MelkhiorVintageComputing/IIsiFPGA/IIsi-to-ztex-gateware/FPMult_15_63_uid2_Freq300_uid3.vhdl

--------------------------------------------------------------------------------
--                       Compressor_23_3_Freq300_uid32
-- VHDL generated for Kintex7 @ 300MHz
-- This operator is part of the Infinite Virtual Library FloPoCoLib
-- All rights reserved 
-- Authors: 
--------------------------------------------------------------------------------
-- combinatorial
-- Clock period (ns): 3.33333
-- Target frequency (MHz): 300
-- Input signals: X1 X0
-- Output signals: R

library ieee;
use ieee.std_logic_1164.all;
use ieee.std_logic_arith.all;
use ieee.std_logic_unsigned.all;
library std;
use std.textio.all;
library work;

entity Compressor_23_3_Freq300_uid32 is
    port (X1 : in  std_logic_vector(1 downto 0);
          X0 : in  std_logic_vector(2 downto 0);
          R : out  std_logic_vector(2 downto 0)   );
end entity;

architecture arch of Compressor_23_3_Freq300_uid32 is
signal X :  std_logic_vector(4 downto 0);
signal R0 :  std_logic_vector(2 downto 0);
begin
   X <= X1 & X0 ;

   with X  select  R0 <= 
      "000" when "00000",
      "001" when "00001" | "00010" | "00100",
      "010" when "00011" | "00101" | "00110" | "01000" | "10000",
      "011" when "00111" | "01001" | "01010" | "01100" | "10001" | "10010" | "10100",
      "100" when "01011" | "01101" | "01110" | "10011" | "10101" | "10110" | "11000",
      "101" when "01111" | "10111" | "11001" | "11010" | "11100",
      "110" when "11011" | "11101" | "11110",
      "111" when "11111",
      "---" when others;
   R <= R0;
end architecture;

--------------------------------------------------------------------------------
--                        Compressor_3_2_Freq300_uid40
-- VHDL generated for Kintex7 @ 300MHz
-- This operator is part of the Infinite Virtual Library FloPoCoLib
-- All rights reserved 
-- Authors: 
--------------------------------------------------------------------------------
-- combinatorial
-- Clock period (ns): 3.33333
-- Target frequency (MHz): 300
-- Input signals: X0
-- Output signals: R

library ieee;
use ieee.std_logic_1164.all;
use ieee.std_logic_arith.all;
use ieee.std_logic_unsigned.all;
library std;
use std.textio.all;
library work;

entity Compressor_3_2_Freq300_uid40 is
    port (X0 : in  std_logic_vector(2 downto 0);
          R : out  std_logic_vector(1 downto 0)   );
end entity;

architecture arch of Compressor_3_2_Freq300_uid40 is
signal X :  std_logic_vector(2 downto 0);
signal R0 :  std_logic_vector(1 downto 0);
begin
   X <= X0 ;

   with X  select  R0 <= 
      "00" when "000",
      "01" when "001" | "010" | "100",
      "10" when "011" | "101" | "110",
      "11" when "111",
      "--" when others;
   R <= R0;
end architecture;

--------------------------------------------------------------------------------
--                       Compressor_14_3_Freq300_uid54
-- VHDL generated for Kintex7 @ 300MHz
-- This operator is part of the Infinite Virtual Library FloPoCoLib
-- All rights reserved 
-- Authors: 
--------------------------------------------------------------------------------
-- combinatorial
-- Clock period (ns): 3.33333
-- Target frequency (MHz): 300
-- Input signals: X1 X0
-- Output signals: R

library ieee;
use ieee.std_logic_1164.all;
use ieee.std_logic_arith.all;
use ieee.std_logic_unsigned.all;
library std;
use std.textio.all;
library work;

entity Compressor_14_3_Freq300_uid54 is
    port (X1 : in  std_logic_vector(0 downto 0);
          X0 : in  std_logic_vector(3 downto 0);
          R : out  std_logic_vector(2 downto 0)   );
end entity;

architecture arch of Compressor_14_3_Freq300_uid54 is
signal X :  std_logic_vector(4 downto 0);
signal R0 :  std_logic_vector(2 downto 0);
begin
   X <= X1 & X0 ;

   with X  select  R0 <= 
      "000" when "00000",
      "001" when "00001" | "00010" | "00100" | "01000",
      "010" when "00011" | "00101" | "00110" | "01001" | "01010" | "01100" | "10000",
      "011" when "00111" | "01011" | "01101" | "01110" | "10001" | "10010" | "10100" | "11000",
      "100" when "01111" | "10011" | "10101" | "10110" | "11001" | "11010" | "11100",
      "101" when "10111" | "11011" | "11101" | "11110",
      "110" when "11111",
      "---" when others;
   R <= R0;
end architecture;

--------------------------------------------------------------------------------
--                        Compressor_6_3_Freq300_uid90
-- VHDL generated for Kintex7 @ 300MHz
-- This operator is part of the Infinite Virtual Library FloPoCoLib
-- All rights reserved 
-- Authors: 
--------------------------------------------------------------------------------
-- combinatorial
-- Clock period (ns): 3.33333
-- Target frequency (MHz): 300
-- Input signals: X0
-- Output signals: R

library ieee;
use ieee.std_logic_1164.all;
use ieee.std_logic_arith.all;
use ieee.std_logic_unsigned.all;
library std;
use std.textio.all;
library work;

entity Compressor_6_3_Freq300_uid90 is
    port (X0 : in  std_logic_vector(5 downto 0);
          R : out  std_logic_vector(2 downto 0)   );
end entity;

architecture arch of Compressor_6_3_Freq300_uid90 is
signal X :  std_logic_vector(5 downto 0);
signal R0 :  std_logic_vector(2 downto 0);
begin
   X <= X0 ;

   with X  select  R0 <= 
      "000" when "000000",
      "001" when "000001" | "000010" | "000100" | "001000" | "010000" | "100000",
      "010" when "000011" | "000101" | "000110" | "001001" | "001010" | "001100" | "010001" | "010010" | "010100" | "011000" | "100001" | "100010" | "100100" | "101000" | "110000",
      "011" when "000111" | "001011" | "001101" | "001110" | "010011" | "010101" | "010110" | "011001" | "011010" | "011100" | "100011" | "100101" | "100110" | "101001" | "101010" | "101100" | "110001" | "110010" | "110100" | "111000",
      "100" when "001111" | "010111" | "011011" | "011101" | "011110" | "100111" | "101011" | "101101" | "101110" | "110011" | "110101" | "110110" | "111001" | "111010" | "111100",
      "101" when "011111" | "101111" | "110111" | "111011" | "111101" | "111110",
      "110" when "111111",
      "---" when others;
   R <= R0;
end architecture;

--------------------------------------------------------------------------------
--                        DSPBlock_24x17_Freq300_uid9
-- VHDL generated for Kintex7 @ 300MHz
-- This operator is part of the Infinite Virtual Library FloPoCoLib
-- All rights reserved 
-- Authors: 
--------------------------------------------------------------------------------
-- Pipeline depth: 0 cycles
-- Clock period (ns): 3.33333
-- Target frequency (MHz): 300
-- Input signals: X Y
-- Output signals: R

library ieee;
use ieee.std_logic_1164.all;
use ieee.numeric_std.all;
library std;
use std.textio.all;
library work;

entity DSPBlock_24x17_Freq300_uid9 is
    port (clk : in std_logic;
          X : in  std_logic_vector(23 downto 0);
          Y : in  std_logic_vector(16 downto 0);
          R : out  std_logic_vector(40 downto 0)   );
end entity;

architecture arch of DSPBlock_24x17_Freq300_uid9 is
signal Mfull :  std_logic_vector(40 downto 0);
signal M :  std_logic_vector(40 downto 0);
begin
   Mfull <= std_logic_vector(unsigned(X) * unsigned(Y)); -- multiplier
   M <= Mfull(40 downto 0);
   R <= M;
end architecture;

--------------------------------------------------------------------------------
--                        DSPBlock_24x17_Freq300_uid11
-- VHDL generated for Kintex7 @ 300MHz
-- This operator is part of the Infinite Virtual Library FloPoCoLib
-- All rights reserved 
-- Authors: 
--------------------------------------------------------------------------------
-- Pipeline depth: 0 cycles
-- Clock period (ns): 3.33333
-- Target frequency (MHz): 300
-- Input signals: X Y
-- Output signals: R

library ieee;
use ieee.std_logic_1164.all;
use ieee.numeric_std.all;
library std;
use std.textio.all;
library work;

entity DSPBlock_24x17_Freq300_uid11 is
    port (clk : in std_logic;
          X : in  std_logic_vector(23 downto 0);
          Y : in  std_logic_vector(16 downto 0);
          R : out  std_logic_vector(40 downto 0)   );
end entity;

architecture arch of DSPBlock_24x17_Freq300_uid11 is
signal Mfull :  std_logic_vector(40 downto 0);
signal M :  std_logic_vector(40 downto 0);
begin
   Mfull <= std_logic_vector(unsigned(X) * unsigned(Y)); -- multiplier
   M <= Mfull(40 downto 0);
   R <= M;
end architecture;

--------------------------------------------------------------------------------
--                        DSPBlock_24x17_Freq300_uid13
-- VHDL generated for Kintex7 @ 300MHz
-- This operator is part of the Infinite Virtual Library FloPoCoLib
-- All rights reserved 
-- Authors: 
--------------------------------------------------------------------------------
-- Pipeline depth: 0 cycles
-- Clock period (ns): 3.33333
-- Target frequency (MHz): 300
-- Input signals: X Y
-- Output signals: R

library ieee;
use ieee.std_logic_1164.all;
use ieee.numeric_std.all;
library std;
use std.textio.all;
library work;

entity DSPBlock_24x17_Freq300_uid13 is
    port (clk : in std_logic;
          X : in  std_logic_vector(23 downto 0);
          Y : in  std_logic_vector(16 downto 0);
          R : out  std_logic_vector(40 downto 0)   );
end entity;

architecture arch of DSPBlock_24x17_Freq300_uid13 is
signal Mfull :  std_logic_vector(40 downto 0);
signal M :  std_logic_vector(40 downto 0);
begin
   Mfull <= std_logic_vector(unsigned(X) * unsigned(Y)); -- multiplier
   M <= Mfull(40 downto 0);
   R <= M;
end architecture;

--------------------------------------------------------------------------------
--                        DSPBlock_24x17_Freq300_uid15
-- VHDL generated for Kintex7 @ 300MHz
-- This operator is part of the Infinite Virtual Library FloPoCoLib
-- All rights reserved 
-- Authors: 
--------------------------------------------------------------------------------
-- Pipeline depth: 0 cycles
-- Clock period (ns): 3.33333
-- Target frequency (MHz): 300
-- Input signals: X Y
-- Output signals: R

library ieee;
use ieee.std_logic_1164.all;
use ieee.numeric_std.all;
library std;
use std.textio.all;
library work;

entity DSPBlock_24x17_Freq300_uid15 is
    port (clk : in std_logic;
          X : in  std_logic_vector(23 downto 0);
          Y : in  std_logic_vector(16 downto 0);
          R : out  std_logic_vector(40 downto 0)   );
end entity;

architecture arch of DSPBlock_24x17_Freq300_uid15 is
signal Mfull :  std_logic_vector(40 downto 0);
signal M :  std_logic_vector(40 downto 0);
begin
   Mfull <= std_logic_vector(unsigned(X) * unsigned(Y)); -- multiplier
   M <= Mfull(40 downto 0);
   R <= M;
end architecture;

--------------------------------------------------------------------------------
--                        DSPBlock_24x17_Freq300_uid17
-- VHDL generated for Kintex7 @ 300MHz
-- This operator is part of the Infinite Virtual Library FloPoCoLib
-- All rights reserved 
-- Authors: 
--------------------------------------------------------------------------------
-- Pipeline depth: 0 cycles
-- Clock period (ns): 3.33333
-- Target frequency (MHz): 300
-- Input signals: X Y
-- Output signals: R

library ieee;
use ieee.std_logic_1164.all;
use ieee.numeric_std.all;
library std;
use std.textio.all;
library work;

entity DSPBlock_24x17_Freq300_uid17 is
    port (clk : in std_logic;
          X : in  std_logic_vector(23 downto 0);
          Y : in  std_logic_vector(16 downto 0);
          R : out  std_logic_vector(40 downto 0)   );
end entity;

architecture arch of DSPBlock_24x17_Freq300_uid17 is
signal Mfull :  std_logic_vector(40 downto 0);
signal M :  std_logic_vector(40 downto 0);
begin
   Mfull <= std_logic_vector(unsigned(X) * unsigned(Y)); -- multiplier
   M <= Mfull(40 downto 0);
   R <= M;
end architecture;

--------------------------------------------------------------------------------
--                        DSPBlock_24x17_Freq300_uid19
-- VHDL generated for Kintex7 @ 300MHz
-- This operator is part of the Infinite Virtual Library FloPoCoLib
-- All rights reserved 
-- Authors: 
--------------------------------------------------------------------------------
-- Pipeline depth: 0 cycles
-- Clock period (ns): 3.33333
-- Target frequency (MHz): 300
-- Input signals: X Y
-- Output signals: R

library ieee;
use ieee.std_logic_1164.all;
use ieee.numeric_std.all;
library std;
use std.textio.all;
library work;

entity DSPBlock_24x17_Freq300_uid19 is
    port (clk : in std_logic;
          X : in  std_logic_vector(23 downto 0);
          Y : in  std_logic_vector(16 downto 0);
          R : out  std_logic_vector(40 downto 0)   );
end entity;

architecture arch of DSPBlock_24x17_Freq300_uid19 is
signal Mfull :  std_logic_vector(40 downto 0);
signal M :  std_logic_vector(40 downto 0);
begin
   Mfull <= std_logic_vector(unsigned(X) * unsigned(Y)); -- multiplier
   M <= Mfull(40 downto 0);
   R <= M;
end architecture;

--------------------------------------------------------------------------------
--                        DSPBlock_16x17_Freq300_uid21
-- VHDL generated for Kintex7 @ 300MHz
-- This operator is part of the Infinite Virtual Library FloPoCoLib
-- All rights reserved 
-- Authors: 
--------------------------------------------------------------------------------
-- Pipeline depth: 0 cycles
-- Clock period (ns): 3.33333
-- Target frequency (MHz): 300
-- Input signals: X Y
-- Output signals: R

library ieee;
use ieee.std_logic_1164.all;
use ieee.numeric_std.all;
library std;
use std.textio.all;
library work;

entity DSPBlock_16x17_Freq300_uid21 is
    port (clk : in std_logic;
          X : in  std_logic_vector(15 downto 0);
          Y : in  std_logic_vector(16 downto 0);
          R : out  std_logic_vector(32 downto 0)   );
end entity;

architecture arch of DSPBlock_16x17_Freq300_uid21 is
signal Mfull :  std_logic_vector(32 downto 0);
signal M :  std_logic_vector(32 downto 0);
begin
   Mfull <= std_logic_vector(unsigned(X) * unsigned(Y)); -- multiplier
   M <= Mfull(32 downto 0);
   R <= M;
end architecture;

--------------------------------------------------------------------------------
--                        DSPBlock_16x24_Freq300_uid23
-- VHDL generated for Kintex7 @ 300MHz
-- This operator is part of the Infinite Virtual Library FloPoCoLib
-- All rights reserved 
-- Authors: 
--------------------------------------------------------------------------------
-- Pipeline depth: 0 cycles
-- Clock period (ns): 3.33333
-- Target frequency (MHz): 300
-- Input signals: X Y
-- Output signals: R

library ieee;
use ieee.std_logic_1164.all;
use ieee.numeric_std.all;
library std;
use std.textio.all;
library work;

entity DSPBlock_16x24_Freq300_uid23 is
    port (clk : in std_logic;
          X : in  std_logic_vector(15 downto 0);
          Y : in  std_logic_vector(23 downto 0);
          R : out  std_logic_vector(39 downto 0)   );
end entity;

architecture arch of DSPBlock_16x24_Freq300_uid23 is
signal Mfull :  std_logic_vector(39 downto 0);
signal M :  std_logic_vector(39 downto 0);
begin
   Mfull <= std_logic_vector(unsigned(X) * unsigned(Y)); -- multiplier
   M <= Mfull(39 downto 0);
   R <= M;
end architecture;

--------------------------------------------------------------------------------
--                        DSPBlock_24x13_Freq300_uid25
-- VHDL generated for Kintex7 @ 300MHz
-- This operator is part of the Infinite Virtual Library FloPoCoLib
-- All rights reserved 
-- Authors: 
--------------------------------------------------------------------------------
-- Pipeline depth: 0 cycles
-- Clock period (ns): 3.33333
-- Target frequency (MHz): 300
-- Input signals: X Y
-- Output signals: R

library ieee;
use ieee.std_logic_1164.all;
use ieee.numeric_std.all;
library std;
use std.textio.all;
library work;

entity DSPBlock_24x13_Freq300_uid25 is
    port (clk : in std_logic;
          X : in  std_logic_vector(23 downto 0);
          Y : in  std_logic_vector(12 downto 0);
          R : out  std_logic_vector(36 downto 0)   );
end entity;

architecture arch of DSPBlock_24x13_Freq300_uid25 is
signal Mfull :  std_logic_vector(36 downto 0);
signal M :  std_logic_vector(36 downto 0);
begin
   Mfull <= std_logic_vector(unsigned(X) * unsigned(Y)); -- multiplier
   M <= Mfull(36 downto 0);
   R <= M;
end architecture;

--------------------------------------------------------------------------------
--                        DSPBlock_24x13_Freq300_uid27
-- VHDL generated for Kintex7 @ 300MHz
-- This operator is part of the Infinite Virtual Library FloPoCoLib
-- All rights reserved 
-- Authors: 
--------------------------------------------------------------------------------
-- Pipeline depth: 0 cycles
-- Clock period (ns): 3.33333
-- Target frequency (MHz): 300
-- Input signals: X Y
-- Output signals: R

library ieee;
use ieee.std_logic_1164.all;
use ieee.numeric_std.all;
library std;
use std.textio.all;
library work;

entity DSPBlock_24x13_Freq300_uid27 is
    port (clk : in std_logic;
          X : in  std_logic_vector(23 downto 0);
          Y : in  std_logic_vector(12 downto 0);
          R : out  std_logic_vector(36 downto 0)   );
end entity;

architecture arch of DSPBlock_24x13_Freq300_uid27 is
signal Mfull :  std_logic_vector(36 downto 0);
signal M :  std_logic_vector(36 downto 0);
begin
   Mfull <= std_logic_vector(unsigned(X) * unsigned(Y)); -- multiplier
   M <= Mfull(36 downto 0);
   R <= M;
end architecture;

--------------------------------------------------------------------------------
--                        DSPBlock_16x23_Freq300_uid29
-- VHDL generated for Kintex7 @ 300MHz
-- This operator is part of the Infinite Virtual Library FloPoCoLib
-- All rights reserved 
-- Authors: 
--------------------------------------------------------------------------------
-- Pipeline depth: 0 cycles
-- Clock period (ns): 3.33333
-- Target frequency (MHz): 300
-- Input signals: X Y
-- Output signals: R

library ieee;
use ieee.std_logic_1164.all;
use ieee.numeric_std.all;
library std;
use std.textio.all;
library work;

entity DSPBlock_16x23_Freq300_uid29 is
    port (clk : in std_logic;
          X : in  std_logic_vector(15 downto 0);
          Y : in  std_logic_vector(22 downto 0);
          R : out  std_logic_vector(38 downto 0)   );
end entity;

architecture arch of DSPBlock_16x23_Freq300_uid29 is
signal Mfull :  std_logic_vector(38 downto 0);
signal M :  std_logic_vector(38 downto 0);
begin
   Mfull <= std_logic_vector(unsigned(X) * unsigned(Y)); -- multiplier
   M <= Mfull(38 downto 0);
   R <= M;
end architecture;

--------------------------------------------------------------------------------
--                        IntAdder_106_Freq300_uid392
-- VHDL generated for Kintex7 @ 300MHz
-- This operator is part of the Infinite Virtual Library FloPoCoLib
-- All rights reserved 
-- Authors: Bogdan Pasca, Florent de Dinechin (2008-2016)
--------------------------------------------------------------------------------
-- Pipeline depth: 2 cycles
-- Clock period (ns): 3.33333
-- Target frequency (MHz): 300
-- Input signals: X Y Cin
-- Output signals: R

library ieee;
use ieee.std_logic_1164.all;
use ieee.std_logic_arith.all;
use ieee.std_logic_unsigned.all;
library std;
use std.textio.all;
library work;

entity IntAdder_106_Freq300_uid392 is
    port (clk : in std_logic;
          X : in  std_logic_vector(105 downto 0);
          Y : in  std_logic_vector(105 downto 0);
          Cin : in  std_logic;
          R : out  std_logic_vector(105 downto 0)   );
end entity;

architecture arch of IntAdder_106_Freq300_uid392 is
signal Rtmp :  std_logic_vector(105 downto 0);
signal X_d1 :  std_logic_vector(105 downto 0);
signal Y_d1 :  std_logic_vector(105 downto 0);
signal Cin_d1, Cin_d2 :  std_logic;
begin
   process(clk)
      begin
         if clk'event and clk = '1' then
            X_d1 <=  X;
            Y_d1 <=  Y;
            Cin_d1 <=  Cin;
            Cin_d2 <=  Cin_d1;
         end if;
      end process;
   Rtmp <= X_d1 + Y_d1 + Cin_d2;
   R <= Rtmp;
end architecture;

--------------------------------------------------------------------------------
--                    IntMultiplier_64x64_128_Freq300_uid5
-- VHDL generated for Kintex7 @ 300MHz
-- This operator is part of the Infinite Virtual Library FloPoCoLib
-- All rights reserved 
-- Authors: Martin Kumm, Florent de Dinechin, Kinga Illyes, Bogdan Popa, Bogdan Pasca, 2012-
--------------------------------------------------------------------------------
-- Pipeline depth: 2 cycles
-- Clock period (ns): 3.33333
-- Target frequency (MHz): 300
-- Input signals: X Y
-- Output signals: R

library ieee;
use ieee.std_logic_1164.all;
use ieee.numeric_std.all;
library std;
use std.textio.all;
library work;

entity IntMultiplier_64x64_128_Freq300_uid5 is
    port (clk : in std_logic;
          X : in  std_logic_vector(63 downto 0);
          Y : in  std_logic_vector(63 downto 0);
          R : out  std_logic_vector(127 downto 0)   );
end entity;

architecture arch of IntMultiplier_64x64_128_Freq300_uid5 is
   component DSPBlock_24x17_Freq300_uid9 is
      port ( clk : in std_logic;
             X : in  std_logic_vector(23 downto 0);
             Y : in  std_logic_vector(16 downto 0);
             R : out  std_logic_vector(40 downto 0)   );
   end component;

   component DSPBlock_24x17_Freq300_uid11 is
      port ( clk : in std_logic;
             X : in  std_logic_vector(23 downto 0);
             Y : in  std_logic_vector(16 downto 0);
             R : out  std_logic_vector(40 downto 0)   );
   end component;

   component DSPBlock_24x17_Freq300_uid13 is
      port ( clk : in std_logic;
             X : in  std_logic_vector(23 downto 0);
             Y : in  std_logic_vector(16 downto 0);
             R : out  std_logic_vector(40 downto 0)   );
   end component;

   component DSPBlock_24x17_Freq300_uid15 is
      port ( clk : in std_logic;
             X : in  std_logic_vector(23 downto 0);
             Y : in  std_logic_vector(16 downto 0);
             R : out  std_logic_vector(40 downto 0)   );
   end component;

   component DSPBlock_24x17_Freq300_uid17 is
      port ( clk : in std_logic;
             X : in  std_logic_vector(23 downto 0);
             Y : in  std_logic_vector(16 downto 0);
             R : out  std_logic_vector(40 downto 0)   );
   end component;

   component DSPBlock_24x17_Freq300_uid19 is
      port ( clk : in std_logic;
             X : in  std_logic_vector(23 downto 0);
             Y : in  std_logic_vector(16 downto 0);
             R : out  std_logic_vector(40 downto 0)   );
   end component;

   component DSPBlock_16x17_Freq300_uid21 is
      port ( clk : in std_logic;
             X : in  std_logic_vector(15 downto 0);
             Y : in  std_logic_vector(16 downto 0);
             R : out  std_logic_vector(32 downto 0)   );
   end component;

   component DSPBlock_16x24_Freq300_uid23 is
      port ( clk : in std_logic;
             X : in  std_logic_vector(15 downto 0);
             Y : in  std_logic_vector(23 downto 0);
             R : out  std_logic_vector(39 downto 0)   );
   end component;

   component DSPBlock_24x13_Freq300_uid25 is
      port ( clk : in std_logic;
             X : in  std_logic_vector(23 downto 0);
             Y : in  std_logic_vector(12 downto 0);
             R : out  std_logic_vector(36 downto 0)   );
   end component;

   component DSPBlock_24x13_Freq300_uid27 is
      port ( clk : in std_logic;
             X : in  std_logic_vector(23 downto 0);
             Y : in  std_logic_vector(12 downto 0);
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
signal bitheapResult_bh7 :  std_logic_vector(127 downto 0);
begin
   process(clk)
      begin
         if clk'event and clk = '1' then
            bh7_w0_0_d1 <=  bh7_w0_0;
            bh7_w1_0_d1 <=  bh7_w1_0;
            bh7_w2_0_d1 <=  bh7_w2_0;
            bh7_w3_0_d1 <=  bh7_w3_0;
            bh7_w4_0_d1 <=  bh7_w4_0;
            bh7_w5_0_d1 <=  bh7_w5_0;
            bh7_w6_0_d1 <=  bh7_w6_0;
            bh7_w7_0_d1 <=  bh7_w7_0;
            bh7_w8_0_d1 <=  bh7_w8_0;
            bh7_w9_0_d1 <=  bh7_w9_0;
            bh7_w10_0_d1 <=  bh7_w10_0;
            bh7_w11_0_d1 <=  bh7_w11_0;
            bh7_w12_0_d1 <=  bh7_w12_0;
            bh7_w13_0_d1 <=  bh7_w13_0;
            bh7_w14_0_d1 <=  bh7_w14_0;
            bh7_w15_0_d1 <=  bh7_w15_0;
            bh7_w16_0_d1 <=  bh7_w16_0;
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
