MelkhiorVintageComputing/IIsiFPGA/IIsi-to-ztex-gateware/FPSqrt_15_63_Freq100.vhdl

--------------------------------------------------------------------------------
--                                FPSqrt_15_63
-- VHDL generated for Kintex7 @ 100MHz
-- This operator is part of the Infinite Virtual Library FloPoCoLib
-- All rights reserved 
-- Authors: 
--------------------------------------------------------------------------------
-- Pipeline depth: 9 cycles
-- Clock period (ns): 10
-- Target frequency (MHz): 100
-- Input signals: X
-- Output signals: R

library ieee;
use ieee.std_logic_1164.all;
use ieee.std_logic_arith.all;
use ieee.std_logic_unsigned.all;
library std;
use std.textio.all;
library work;

entity FPSqrt_15_63 is
    port (clk : in std_logic;
          X : in  std_logic_vector(15+63+2 downto 0);
          R : out  std_logic_vector(15+63+2 downto 0)   );
end entity;

architecture arch of FPSqrt_15_63 is
signal fracX :  std_logic_vector(62 downto 0);
signal eRn0 :  std_logic_vector(14 downto 0);
signal xsX :  std_logic_vector(2 downto 0);
signal eRn1, eRn1_d1, eRn1_d2, eRn1_d3, eRn1_d4, eRn1_d5, eRn1_d6, eRn1_d7, eRn1_d8, eRn1_d9 :  std_logic_vector(14 downto 0);
signal fracXnorm :  std_logic_vector(66 downto 0);
signal S0 :  std_logic_vector(1 downto 0);
signal T1 :  std_logic_vector(66 downto 0);
signal d1 :  std_logic;
signal T1s :  std_logic_vector(67 downto 0);
signal T1s_h :  std_logic_vector(5 downto 0);
signal T1s_l :  std_logic_vector(61 downto 0);
signal U1 :  std_logic_vector(5 downto 0);
signal T3_h :  std_logic_vector(5 downto 0);
signal T2 :  std_logic_vector(66 downto 0);
signal S1 :  std_logic_vector(2 downto 0);
signal d2 :  std_logic;
signal T2s :  std_logic_vector(67 downto 0);
signal T2s_h :  std_logic_vector(6 downto 0);
signal T2s_l :  std_logic_vector(60 downto 0);
signal U2 :  std_logic_vector(6 downto 0);
signal T4_h :  std_logic_vector(6 downto 0);
signal T3 :  std_logic_vector(66 downto 0);
signal S2 :  std_logic_vector(3 downto 0);
signal d3 :  std_logic;
signal T3s :  std_logic_vector(67 downto 0);
signal T3s_h :  std_logic_vector(7 downto 0);
signal T3s_l :  std_logic_vector(59 downto 0);
signal U3 :  std_logic_vector(7 downto 0);
signal T5_h :  std_logic_vector(7 downto 0);
signal T4 :  std_logic_vector(66 downto 0);
signal S3 :  std_logic_vector(4 downto 0);
signal d4 :  std_logic;
signal T4s :  std_logic_vector(67 downto 0);
signal T4s_h :  std_logic_vector(8 downto 0);
signal T4s_l :  std_logic_vector(58 downto 0);
signal U4 :  std_logic_vector(8 downto 0);
signal T6_h :  std_logic_vector(8 downto 0);
signal T5 :  std_logic_vector(66 downto 0);
signal S4 :  std_logic_vector(5 downto 0);
signal d5 :  std_logic;
signal T5s :  std_logic_vector(67 downto 0);
signal T5s_h :  std_logic_vector(9 downto 0);
signal T5s_l :  std_logic_vector(57 downto 0);
signal U5 :  std_logic_vector(9 downto 0);
signal T7_h :  std_logic_vector(9 downto 0);
signal T6 :  std_logic_vector(66 downto 0);
signal S5 :  std_logic_vector(6 downto 0);
signal d6 :  std_logic;
signal T6s :  std_logic_vector(67 downto 0);
signal T6s_h :  std_logic_vector(10 downto 0);
signal T6s_l :  std_logic_vector(56 downto 0);
signal U6 :  std_logic_vector(10 downto 0);
signal T8_h :  std_logic_vector(10 downto 0);
signal T7 :  std_logic_vector(66 downto 0);
signal S6 :  std_logic_vector(7 downto 0);
signal d7 :  std_logic;
signal T7s :  std_logic_vector(67 downto 0);
signal T7s_h :  std_logic_vector(11 downto 0);
signal T7s_l :  std_logic_vector(55 downto 0);
signal U7 :  std_logic_vector(11 downto 0);
signal T9_h :  std_logic_vector(11 downto 0);
signal T8 :  std_logic_vector(66 downto 0);
signal S7 :  std_logic_vector(8 downto 0);
signal d8 :  std_logic;
signal T8s :  std_logic_vector(67 downto 0);
signal T8s_h :  std_logic_vector(12 downto 0);
signal T8s_l :  std_logic_vector(54 downto 0);
signal U8 :  std_logic_vector(12 downto 0);
signal T10_h :  std_logic_vector(12 downto 0);
signal T9 :  std_logic_vector(66 downto 0);
signal S8 :  std_logic_vector(9 downto 0);
signal d9, d9_d1 :  std_logic;
signal T9s :  std_logic_vector(67 downto 0);
signal T9s_h, T9s_h_d1 :  std_logic_vector(13 downto 0);
signal T9s_l, T9s_l_d1 :  std_logic_vector(53 downto 0);
signal U9, U9_d1 :  std_logic_vector(13 downto 0);
signal T11_h :  std_logic_vector(13 downto 0);
signal T10 :  std_logic_vector(66 downto 0);
signal S9, S9_d1 :  std_logic_vector(10 downto 0);
signal d10 :  std_logic;
signal T10s :  std_logic_vector(67 downto 0);
signal T10s_h :  std_logic_vector(14 downto 0);
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
signal fR :  std_logic_vector(62 downto 0);
signal round :  std_logic;
signal fRrnd :  std_logic_vector(62 downto 0);
signal Rn2 :  std_logic_vector(77 downto 0);
signal xsR, xsR_d1, xsR_d2, xsR_d3, xsR_d4, xsR_d5, xsR_d6, xsR_d7, xsR_d8, xsR_d9 :  std_logic_vector(2 downto 0);
begin
   process(clk)
      begin
         if clk'event and clk = '1' then
            eRn1_d1 <=  eRn1;
            eRn1_d2 <=  eRn1_d1;
            eRn1_d3 <=  eRn1_d2;
            eRn1_d4 <=  eRn1_d3;
            eRn1_d5 <=  eRn1_d4;
            eRn1_d6 <=  eRn1_d5;
            eRn1_d7 <=  eRn1_d6;
            eRn1_d8 <=  eRn1_d7;
            eRn1_d9 <=  eRn1_d8;
            d9_d1 <=  d9;
            T9s_h_d1 <=  T9s_h;
            T9s_l_d1 <=  T9s_l;
            U9_d1 <=  U9;
            S9_d1 <=  S9;
            d17_d1 <=  d17;
            T17s_h_d1 <=  T17s_h;
            T17s_l_d1 <=  T17s_l;
            U17_d1 <=  U17;
            S17_d1 <=  S17;
            d25_d1 <=  d25;
            T25s_h_d1 <=  T25s_h;
            T25s_l_d1 <=  T25s_l;
            U25_d1 <=  U25;
            S25_d1 <=  S25;
            d32_d1 <=  d32;
            T32s_h_d1 <=  T32s_h;
            T32s_l_d1 <=  T32s_l;
            U32_d1 <=  U32;
            S32_d1 <=  S32;
            d39_d1 <=  d39;
            T39s_h_d1 <=  T39s_h;
            T39s_l_d1 <=  T39s_l;
            U39_d1 <=  U39;
            S39_d1 <=  S39;
            d45_d1 <=  d45;
            T45s_h_d1 <=  T45s_h;
            T45s_l_d1 <=  T45s_l;
            U45_d1 <=  U45;
            S45_d1 <=  S45;
            d52_d1 <=  d52;
            T52s_h_d1 <=  T52s_h;
            T52s_l_d1 <=  T52s_l;
            U52_d1 <=  U52;
            S52_d1 <=  S52;
            d57_d1 <=  d57;
            T57s_h_d1 <=  T57s_h;
            T57s_l_d1 <=  T57s_l;
            U57_d1 <=  U57;
            S57_d1 <=  S57;
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
            xsR_d1 <=  xsR;
            xsR_d2 <=  xsR_d1;
            xsR_d3 <=  xsR_d2;
            xsR_d4 <=  xsR_d3;
            xsR_d5 <=  xsR_d4;
            xsR_d6 <=  xsR_d5;
            xsR_d7 <=  xsR_d6;
            xsR_d8 <=  xsR_d7;
            xsR_d9 <=  xsR_d8;
         end if;
      end process;
   fracX <= X(62 downto 0); -- fraction
   eRn0 <= "0" & X(77 downto 64); -- exponent
   xsX <= X(80 downto 78); -- exception and sign
   eRn1 <= eRn0 + ("00" & (12 downto 0 => '1')) + X(63);
   fracXnorm <= "1" & fracX & "000" when X(63) = '0' else
         "01" & fracX&"00"; -- pre-normalization
   S0 <= "01";
   T1 <= ("0111" + fracXnorm(66 downto 63)) & fracXnorm(62 downto 0);
   -- now implementing the recurrence 
   --  this is a binary non-restoring algorithm, see ASA book
   -- Step 2
   d1 <= not T1(66); --  bit of weight -1
   T1s <= T1 & "0";
   T1s_h <= T1s(67 downto 62);
   T1s_l <= T1s(61 downto 0);
   U1 <=  "0" & S0 & d1 & (not d1) & "1"; 
   T3_h <=   T1s_h - U1 when d1='1'
        else T1s_h + U1;
   T2 <= T3_h(4 downto 0) & T1s_l;
   S1 <= S0 & d1; -- here -1 becomes 0 and 1 becomes 1
   -- Step 3
   d2 <= not T2(66); --  bit of weight -2
   T2s <= T2 & "0";
   T2s_h <= T2s(67 downto 61);
   T2s_l <= T2s(60 downto 0);
   U2 <=  "0" & S1 & d2 & (not d2) & "1"; 
   T4_h <=   T2s_h - U2 when d2='1'
        else T2s_h + U2;
   T3 <= T4_h(5 downto 0) & T2s_l;
   S2 <= S1 & d2; -- here -1 becomes 0 and 1 becomes 1
   -- Step 4
   d3 <= not T3(66); --  bit of weight -3
   T3s <= T3 & "0";
   T3s_h <= T3s(67 downto 60);
   T3s_l <= T3s(59 downto 0);
   U3 <=  "0" & S2 & d3 & (not d3) & "1"; 
   T5_h <=   T3s_h - U3 when d3='1'
        else T3s_h + U3;
   T4 <= T5_h(6 downto 0) & T3s_l;
   S3 <= S2 & d3; -- here -1 becomes 0 and 1 becomes 1
   -- Step 5
   d4 <= not T4(66); --  bit of weight -4
   T4s <= T4 & "0";
   T4s_h <= T4s(67 downto 59);
   T4s_l <= T4s(58 downto 0);
   U4 <=  "0" & S3 & d4 & (not d4) & "1"; 
   T6_h <=   T4s_h - U4 when d4='1'
        else T4s_h + U4;
   T5 <= T6_h(7 downto 0) & T4s_l;
   S4 <= S3 & d4; -- here -1 becomes 0 and 1 becomes 1
   -- Step 6
   d5 <= not T5(66); --  bit of weight -5
   T5s <= T5 & "0";
   T5s_h <= T5s(67 downto 58);
   T5s_l <= T5s(57 downto 0);
   U5 <=  "0" & S4 & d5 & (not d5) & "1"; 
   T7_h <=   T5s_h - U5 when d5='1'
        else T5s_h + U5;
   T6 <= T7_h(8 downto 0) & T5s_l;
   S5 <= S4 & d5; -- here -1 becomes 0 and 1 becomes 1
   -- Step 7
   d6 <= not T6(66); --  bit of weight -6
   T6s <= T6 & "0";
   T6s_h <= T6s(67 downto 57);
   T6s_l <= T6s(56 downto 0);
   U6 <=  "0" & S5 & d6 & (not d6) & "1"; 
   T8_h <=   T6s_h - U6 when d6='1'
        else T6s_h + U6;
   T7 <= T8_h(9 downto 0) & T6s_l;
   S6 <= S5 & d6; -- here -1 becomes 0 and 1 becomes 1
   -- Step 8
   d7 <= not T7(66); --  bit of weight -7
   T7s <= T7 & "0";
   T7s_h <= T7s(67 downto 56);
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
   T62_h <=   T60s_h - U60 when d60='1'
        else T60s_h + U60;
   T61 <= T62_h(63 downto 0) & T60s_l;
   S60 <= S59 & d60; -- here -1 becomes 0 and 1 becomes 1
   -- Step 62
   d61 <= not T61(66); --  bit of weight -61
   T61s <= T61 & "0";
   T61s_h <= T61s(67 downto 2);
   T61s_l <= T61s(1 downto 0);
   U61 <=  "0" & S60 & d61 & (not d61) & "1"; 
   T63_h <=   T61s_h - U61 when d61='1'
        else T61s_h + U61;
   T62 <= T63_h(64 downto 0) & T61s_l;
   S61 <= S60 & d61; -- here -1 becomes 0 and 1 becomes 1
   -- Step 63
   d62 <= not T62(66); --  bit of weight -62
   T62s <= T62 & "0";
   T62s_h <= T62s(67 downto 1);
   T62s_l <= T62s(0 downto 0);
   U62 <=  "0" & S61 & d62 & (not d62) & "1"; 
   T64_h <=   T62s_h - U62 when d62='1'
        else T62s_h + U62;
   T63 <= T64_h(65 downto 0) & T62s_l;
   S62 <= S61 & d62; -- here -1 becomes 0 and 1 becomes 1
   -- Step 64
   d63 <= not T63(66); --  bit of weight -63
   T63s <= T63 & "0";
   T63s_h <= T63s(67 downto 0);
   U63 <=  "0" & S62 & d63 & (not d63) & "1"; 
   T65_h <=   T63s_h_d1 - U63_d1 when d63_d1='1'
        else T63s_h_d1 + U63_d1;
   T64 <= T65_h(66 downto 0);
   S63 <= S62 & d63; -- here -1 becomes 0 and 1 becomes 1
   d65 <= not T64(66) ; -- the sign of the remainder will become the round bit
   mR <= S63_d1 & d65; -- result significand
   fR <= mR(63 downto 1);-- removing leading 1
   round <= mR(0); -- round bit
   fRrnd <= fR + ((62 downto 1 => '0') & round); -- rounding sqrt never changes exponents 
   Rn2 <= eRn1_d9 & fRrnd;
   -- sign and exception processing
   with xsX  select 
      xsR <= "010"  when "010",  -- normal case
             "100"  when "100",  -- +infty
             "000"  when "000",  -- +0
             "001"  when "001",  -- the infamous sqrt(-0)=-0
             "110"  when others; -- return NaN
   R <= xsR_d9 & Rn2; 
end architecture;
